TheCaveCz/kit-alarm-clock/doc/pictures/IMG_7124.JPG

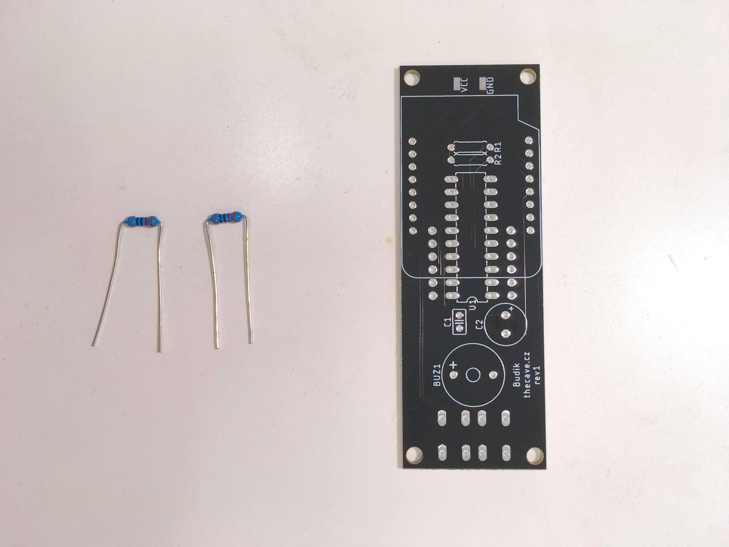
doc/pictures/IMG_7124.JPG
