TheCaveCz/kit-alarm-clock/doc/pictures/IMG_7126.JPG

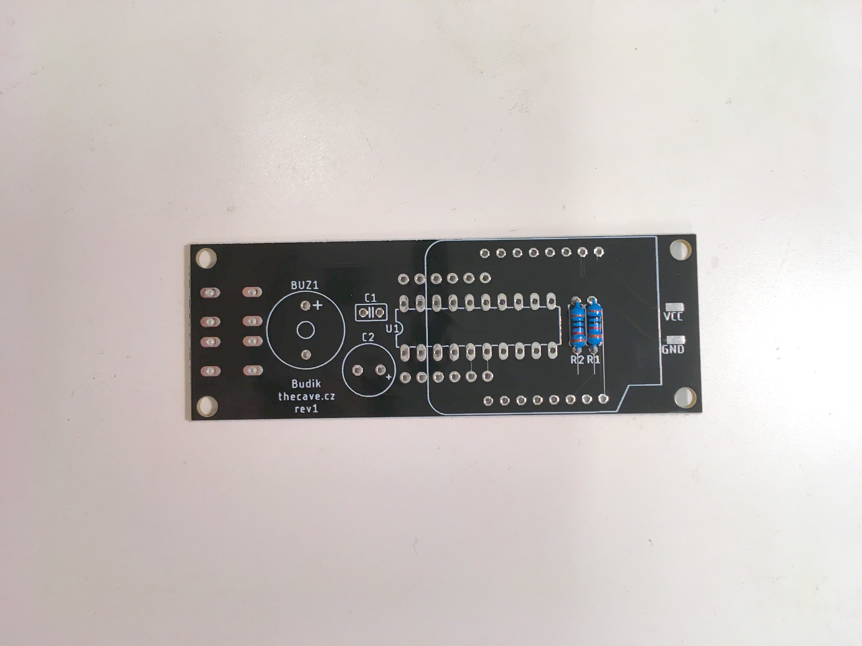
doc/pictures/IMG_7126.JPG
