TheCaveCz/kit-alarm-clock/doc/pictures/IMG_7127.JPG

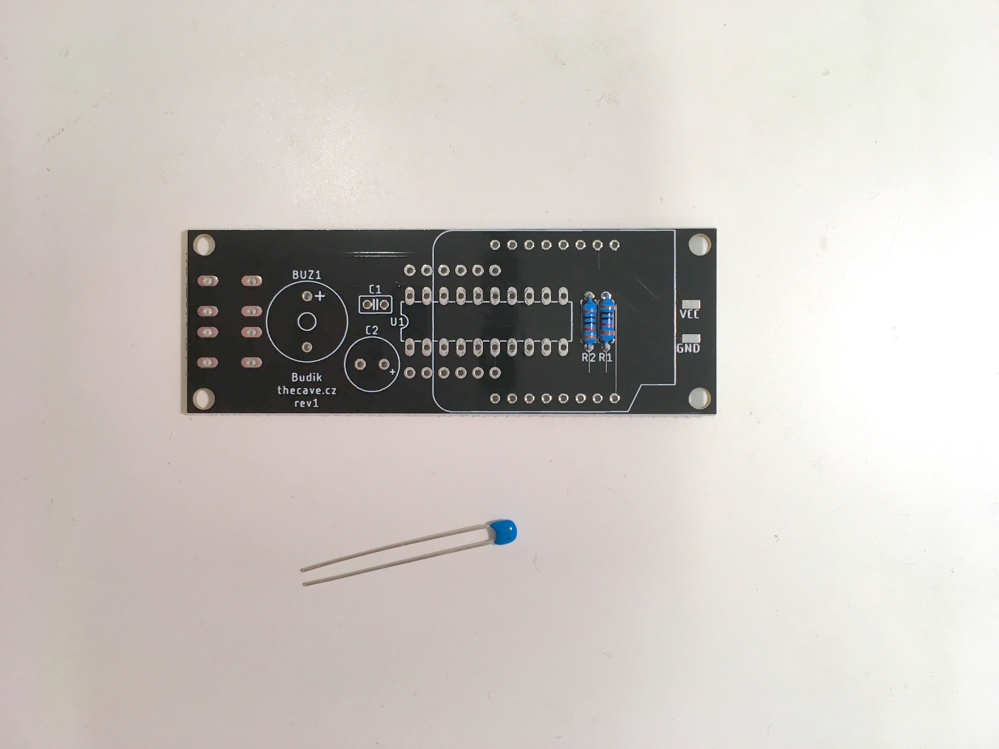
doc/pictures/IMG_7127.JPG
