TheCaveCz/kit-alarm-clock/doc/pictures/IMG_7128.JPG

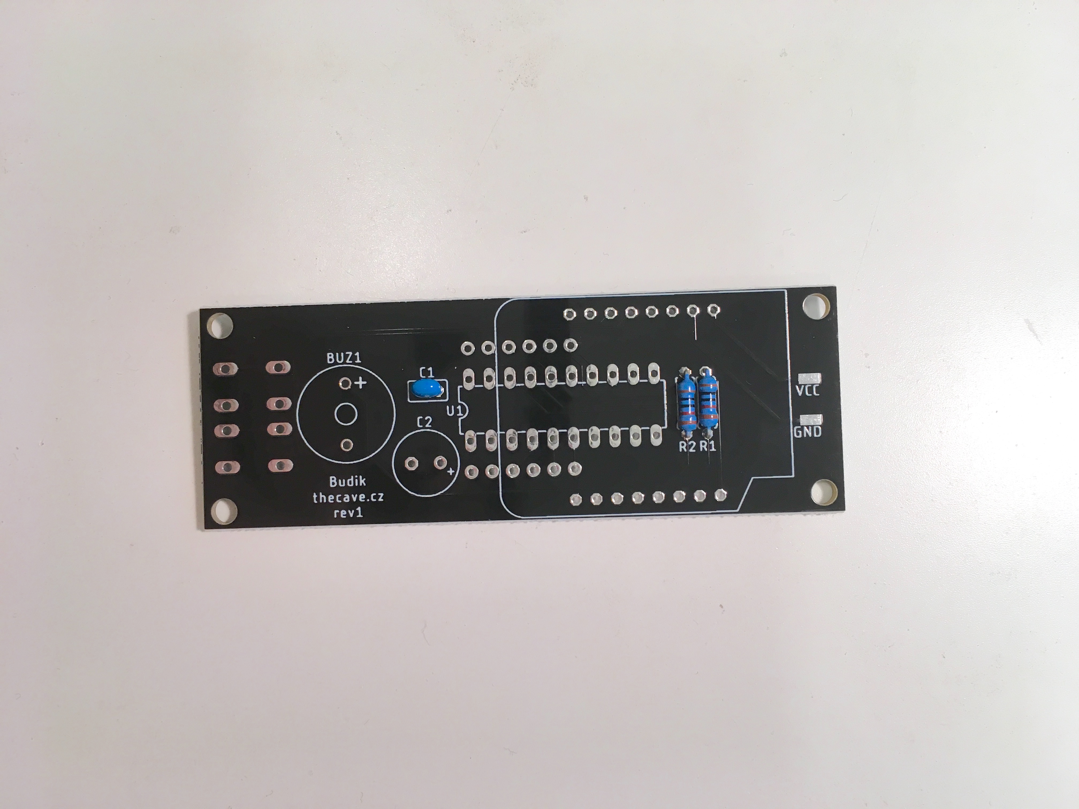
doc/pictures/IMG_7128.JPG
