TheCaveCz/kit-alarm-clock/doc/pictures/IMG_7130.JPG

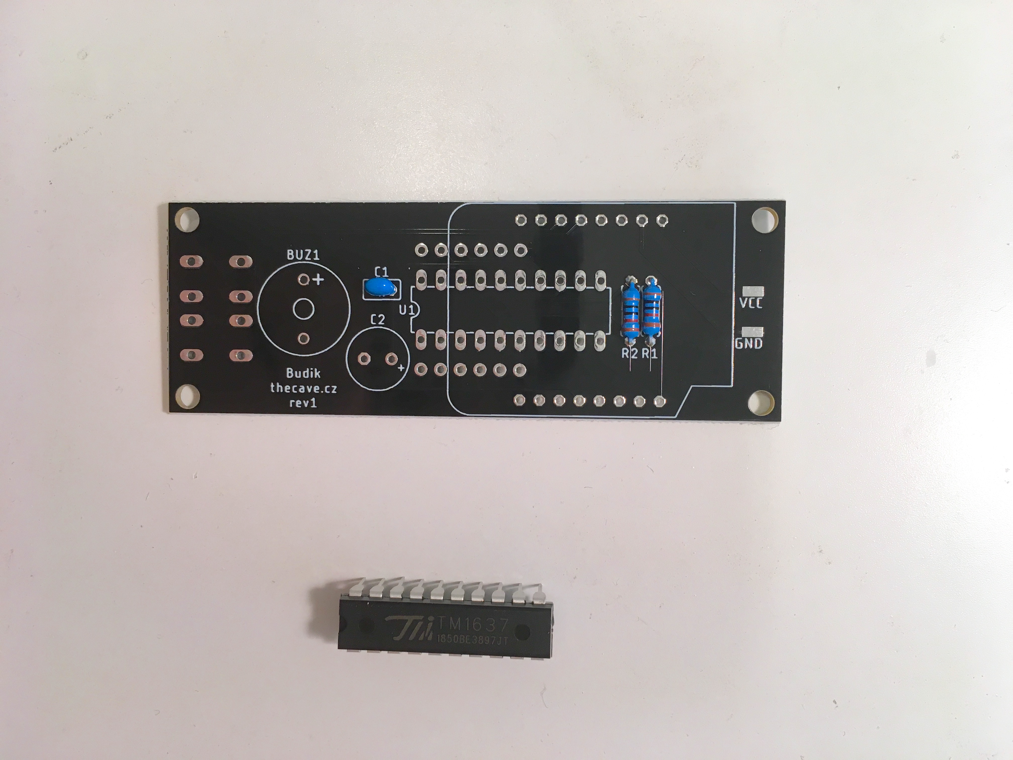
doc/pictures/IMG_7130.JPG
