TheCaveCz/kit-alarm-clock/doc/pictures/IMG_7131.JPG

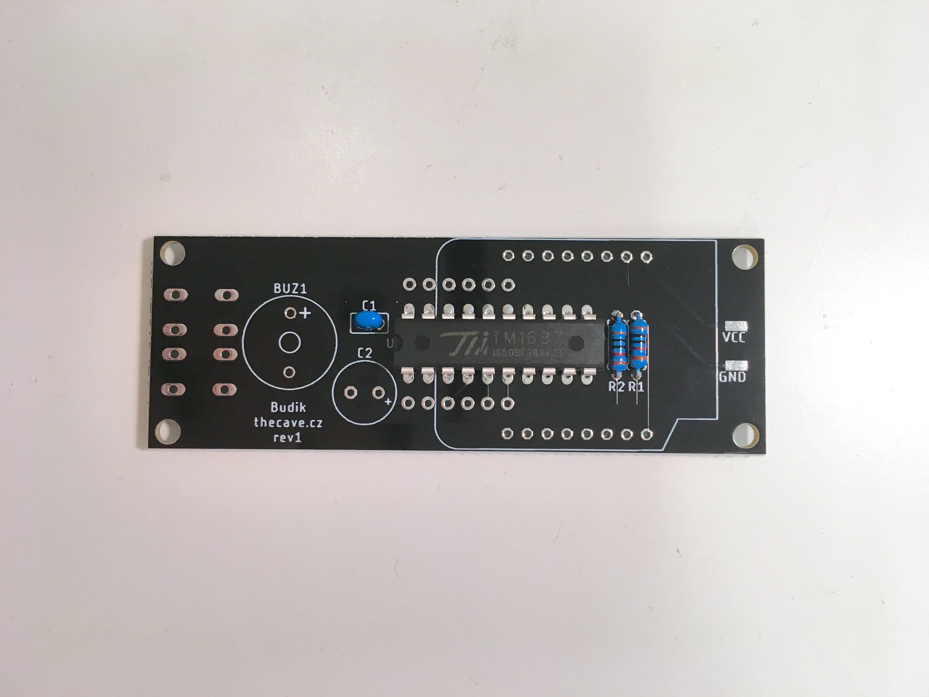
doc/pictures/IMG_7131.JPG
