TheCaveCz/kit-alarm-clock/doc/pictures/IMG_7133.JPG

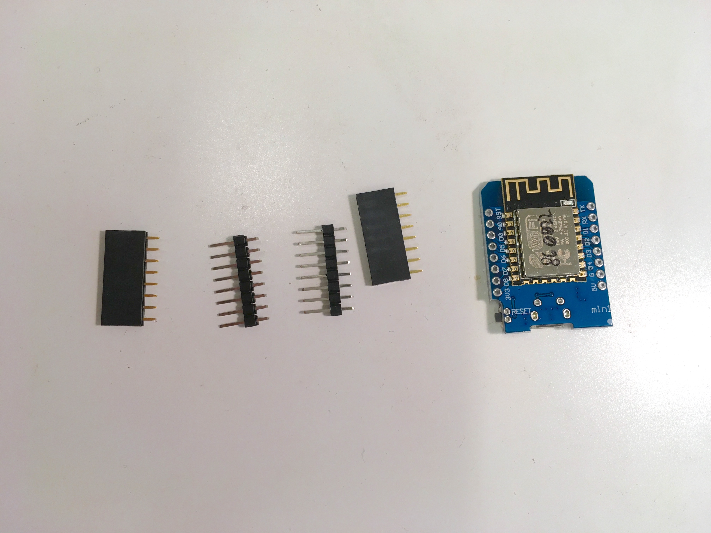
doc/pictures/IMG_7133.JPG
