TheCaveCz/kit-alarm-clock/doc/pictures/IMG_7136.JPG

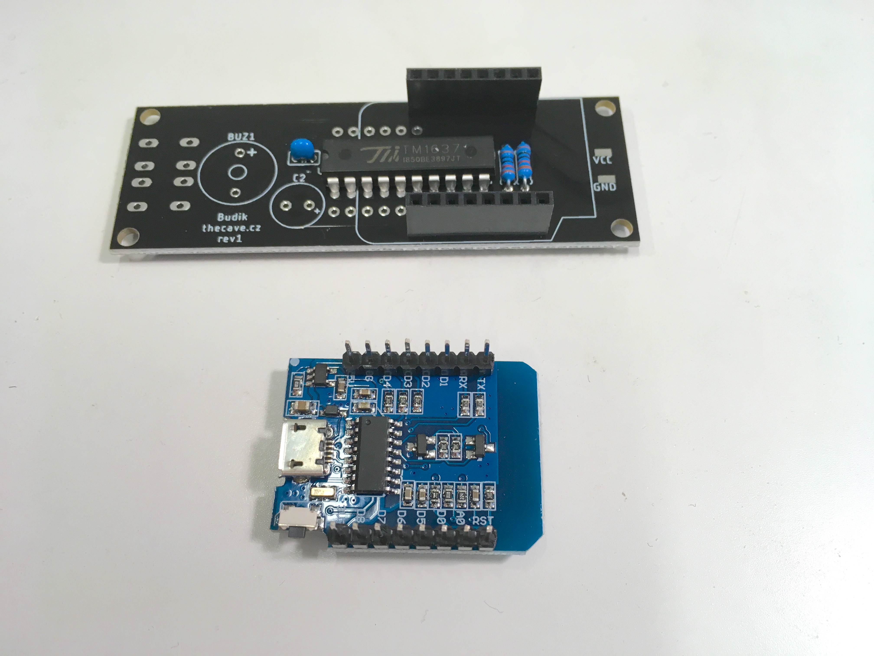
doc/pictures/IMG_7136.JPG
