TheCaveCz/kit-alarm-clock/doc/pictures/IMG_7137.JPG

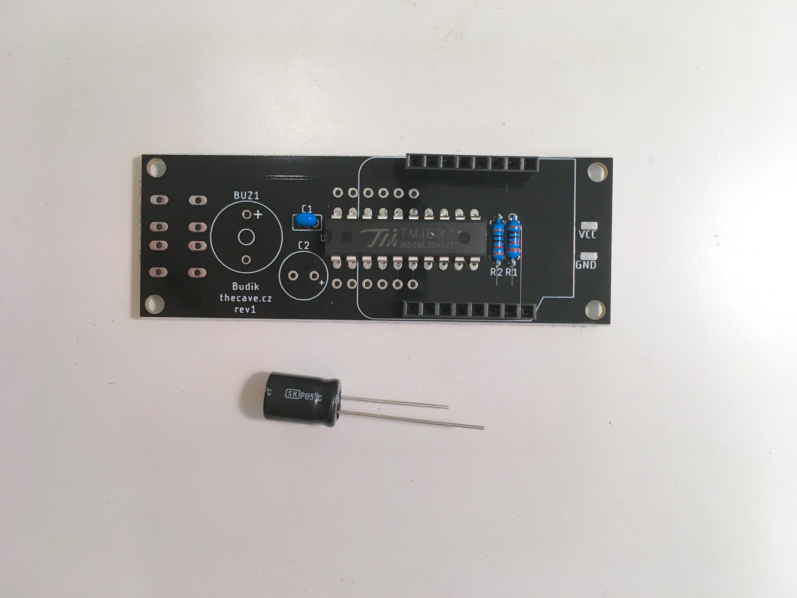
doc/pictures/IMG_7137.JPG
