TheCaveCz/kit-alarm-clock/doc/pictures/IMG_7138.JPG

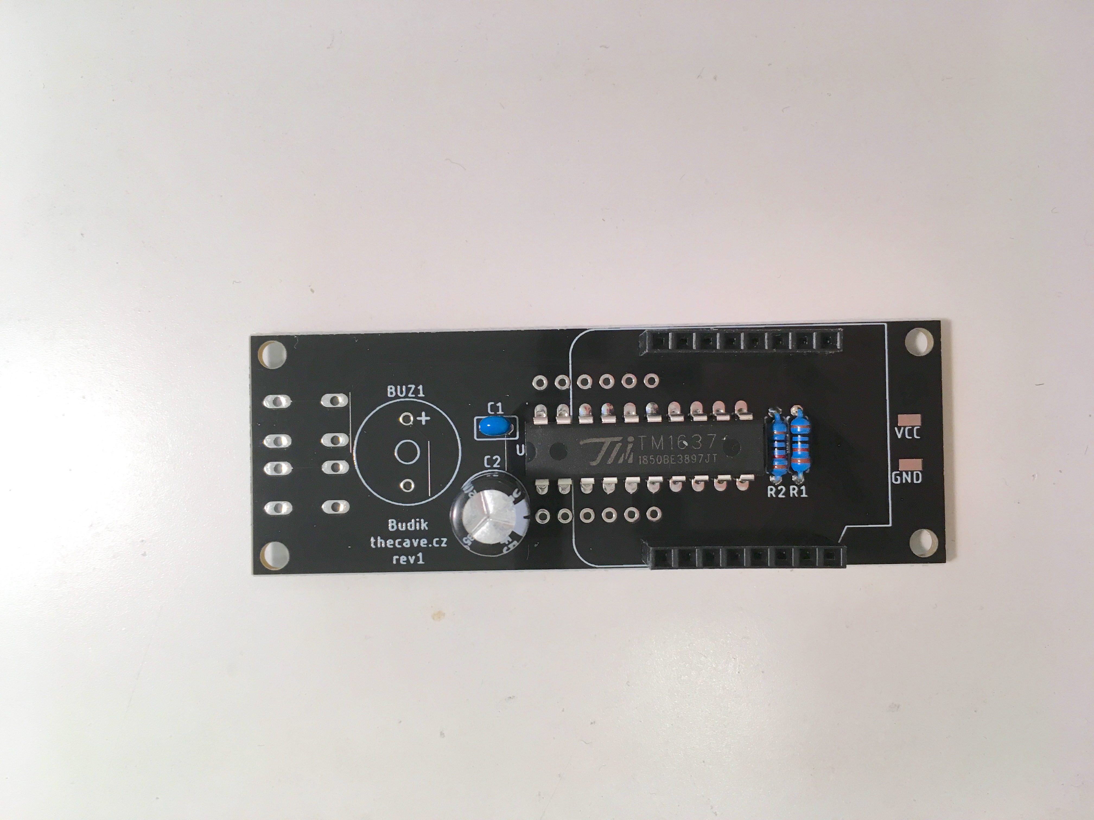
doc/pictures/IMG_7138.JPG
