TheCaveCz/kit-alarm-clock/doc/pictures/IMG_7139.JPG

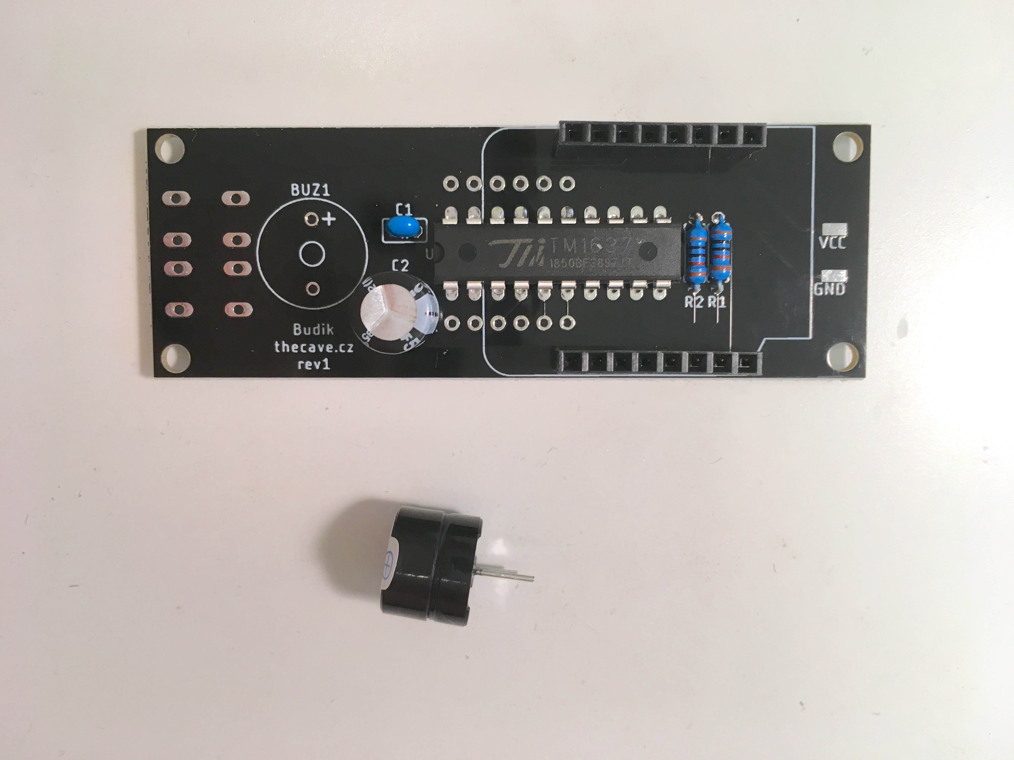
doc/pictures/IMG_7139.JPG
