TheCaveCz/kit-alarm-clock/doc/pictures/IMG_7141.JPG

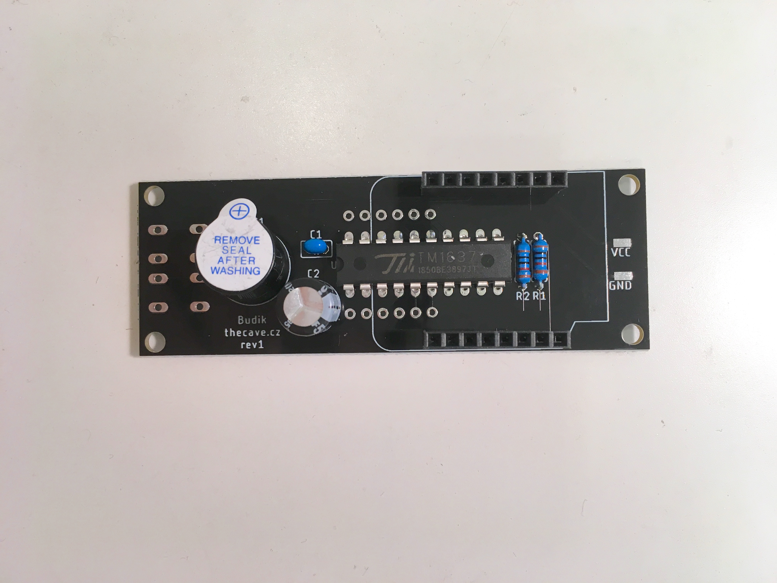
doc/pictures/IMG_7141.JPG
