TheCaveCz/kit-alarm-clock/doc/pictures/IMG_7142.JPG

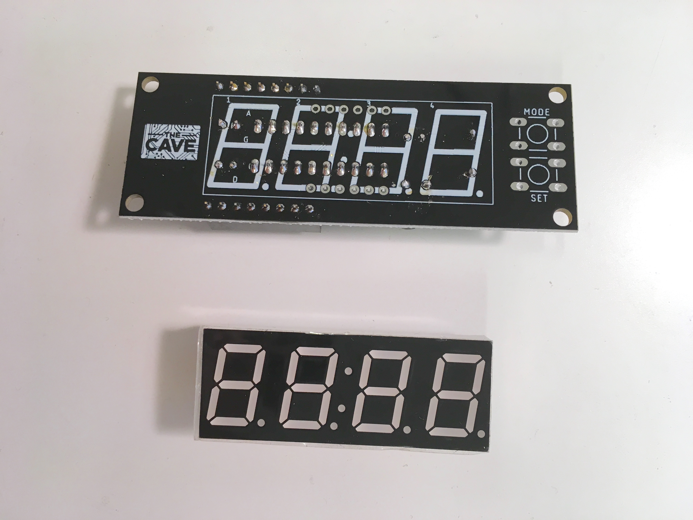
doc/pictures/IMG_7142.JPG
