TheCaveCz/kit-alarm-clock/doc/pictures/IMG_7143.JPG

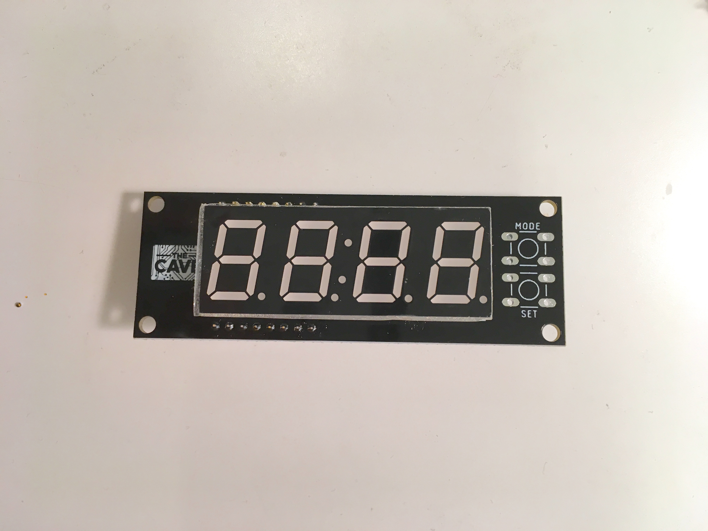
doc/pictures/IMG_7143.JPG
