TheCaveCz/kit-alarm-clock/doc/pictures/IMG_7144.JPG

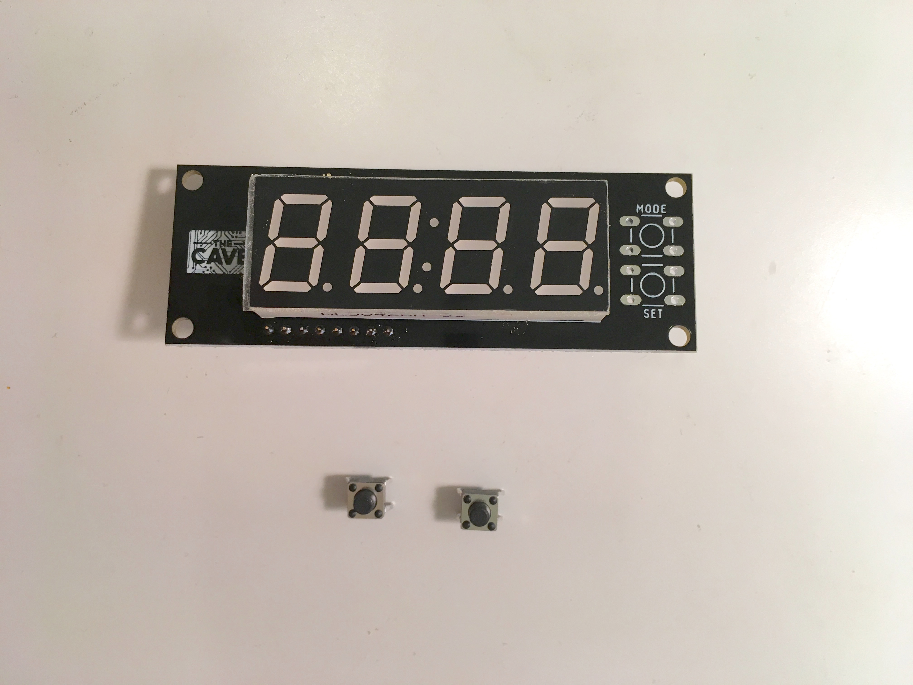
doc/pictures/IMG_7144.JPG
