TheCaveCz/kit-alarm-clock/doc/pictures/IMG_7145.JPG

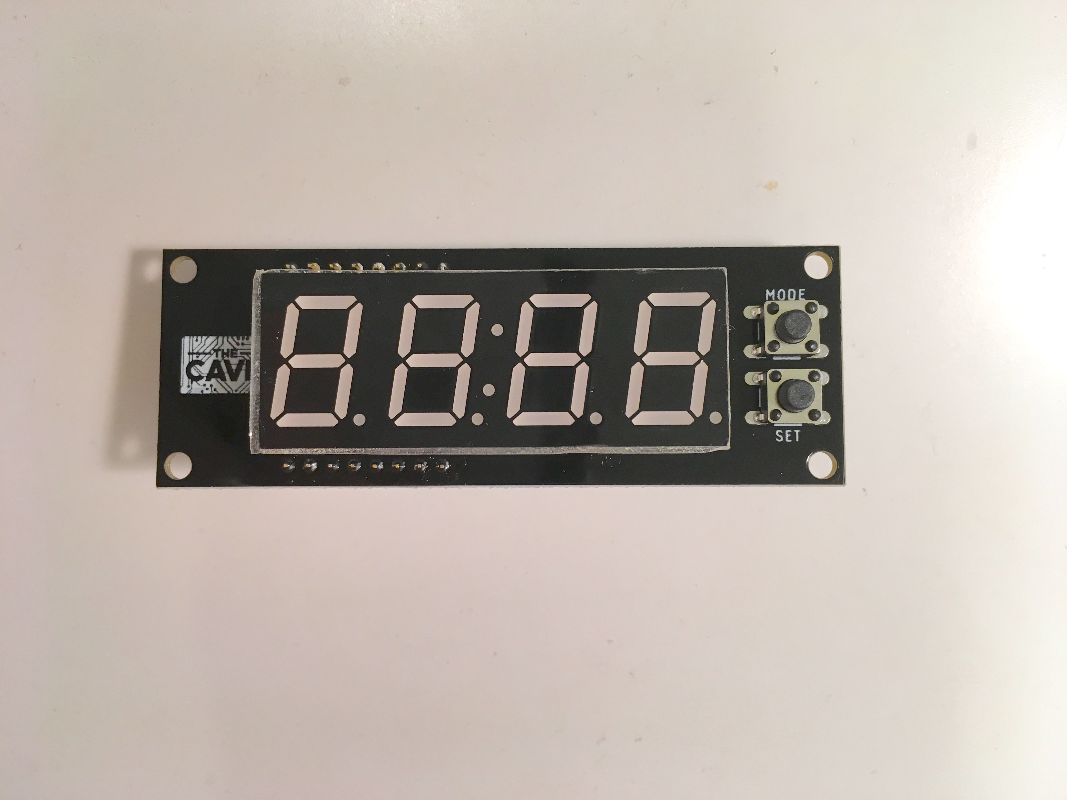
doc/pictures/IMG_7145.JPG
